Blinkinlabs/BlinkyTape/production/TestProgram_Beaglebone/menus.py

menus = {
'pcba_test' : [
          ('Run all Tests'           , ['test_power_on',
                                        'test_bootloader',
                                        'test_functional']),
          ('Power on Test'           , 'test_power_on'),
          ('Flash Bootloader test'   , 'test_bootloader'),
          ('Function Test'           , 'test_functional'),
	],
}
